buttonbugs/UA-AIAA-Payload-2026/data/rocket_20260618121819CDT/graph_pressure_temp.png

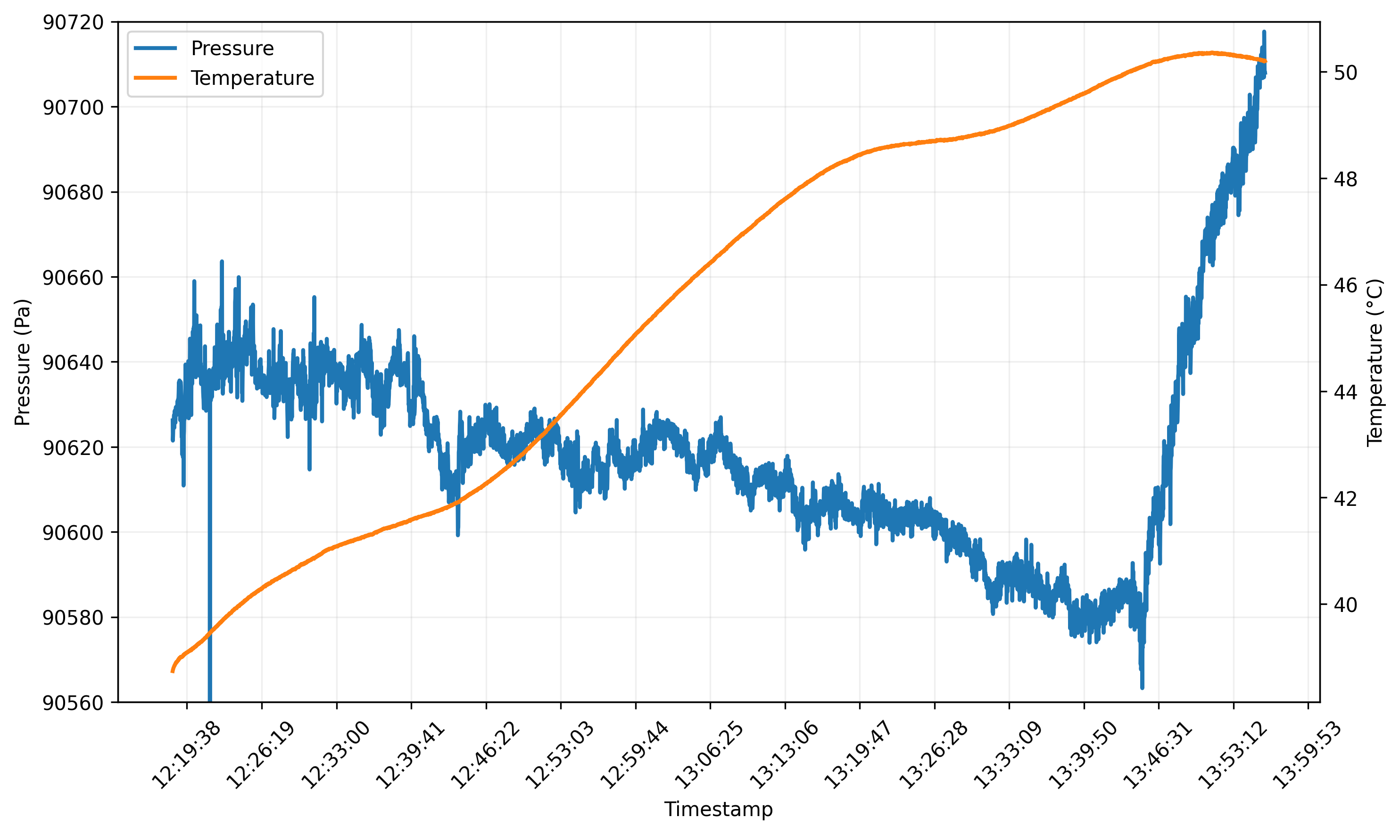
data/rocket_20260618121819CDT/graph_pressure_temp.png
