buttonbugs/UA-AIAA-Payload-2026/data/rocket_20260618121819CDT/graph_ultrasonic.png

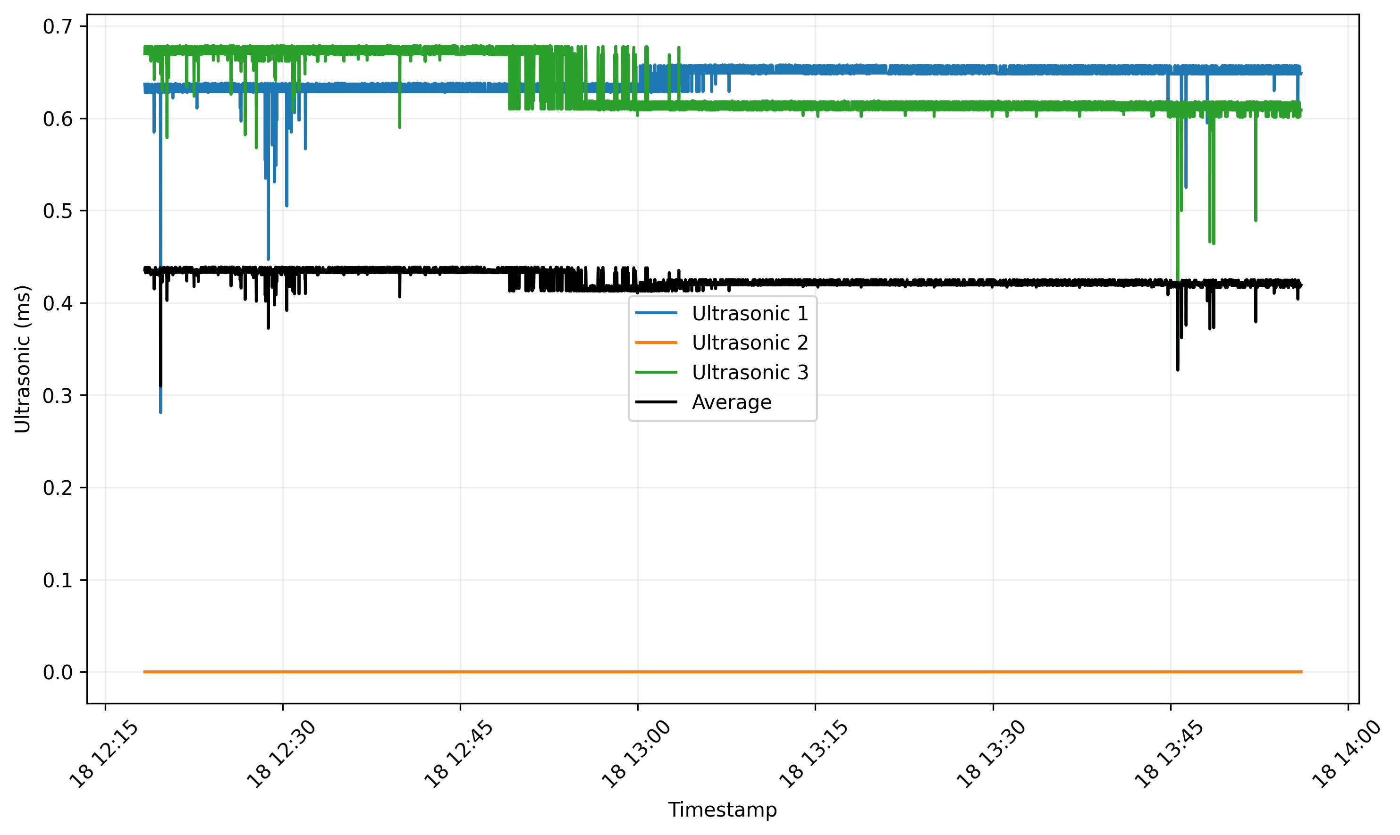
data/rocket_20260618121819CDT/graph_ultrasonic.png
