buttonbugs/UA-AIAA-Payload-2026/data/testing_20260617142200CDT/DATA_000.CSV

Timestamp (ms) | Ozone (PPB) | Air quality (VOC) | Accelerometer X (milli-g) | Accelerometer Y (milli-g) | Accelerometer Z (milli-g) | Gyroscope X (deg/s) | Gyroscope Y (deg/s) | Gyroscope Z (deg/s) | Magnetometer X (uT) | Magnetometer Y (uT) | Magnetometer Z (uT) | IMU Temperature (C) | BME280 Temperature (C) | Pressure (Pa) | Humidity (%RH) | Ultrasonic 1 (ms) | Ultrasonic 2 (ms) | Ultrasonic 3 (ms) | Vibration 1 Period (ms) | Vibration 2 Period (ms)
Timestamp (ms) | Ozone (PPB) | Air quality (VOC) | Accelerometer X (milli-g) | Accelerometer Y (milli-g) | Accelerometer Z (milli-g) | Gyroscope X (deg/s) | Gyroscope Y (deg/s) | Gyroscope Z (deg/s) | Magnetometer X (uT) | Magnetometer Y (uT) | Magnetometer Z (uT) | IMU Temperature (C) | BME280 Temperature (C) | Pressure (Pa) | Humidity (%RH) | Ultrasonic 1 (ms) | Ultrasonic 2 (ms) | Ultrasonic 3 (ms) | Vibration 1 Period (ms) | Vibration 2 Period (ms)
1140 | 0 | 0 | -2.3681639E+02 | 1.0917969E+03 | 9.3261711E+01 | -5.7480917E+00 | -2.9312978E+00 | -4.4198475E+00 | -2.4000000E+01 | -2.1900002E+01 | -4.1400002E+01 | 2.8748526E+01 | 2.5780001E+01 | 9.0634344E+04 | 3.3261719E+01 | 6.9000000E-01 | 0.0000000E+00 | 6.4399999E-01 | 0 | 0
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
