buttonbugs/UA-AIAA-Payload-2026/data/testing_20260617142200CDT/DATA_001.CSV

Timestamp (ms) | Ozone (PPB) | Air quality (VOC) | Accelerometer X (milli-g) | Accelerometer Y (milli-g) | Accelerometer Z (milli-g) | Gyroscope X (deg/s) | Gyroscope Y (deg/s) | Gyroscope Z (deg/s) | Magnetometer X (uT) | Magnetometer Y (uT) | Magnetometer Z (uT) | IMU Temperature (C) | BME280 Temperature (C) | Pressure (Pa) | Humidity (%RH) | Ultrasonic 1 (ms) | Ultrasonic 2 (ms) | Ultrasonic 3 (ms) | Vibration 1 Period (ms) | Vibration 2 Period (ms)
Timestamp (ms) | Ozone (PPB) | Air quality (VOC) | Accelerometer X (milli-g) | Accelerometer Y (milli-g) | Accelerometer Z (milli-g) | Gyroscope X (deg/s) | Gyroscope Y (deg/s) | Gyroscope Z (deg/s) | Magnetometer X (uT) | Magnetometer Y (uT) | Magnetometer Z (uT) | IMU Temperature (C) | BME280 Temperature (C) | Pressure (Pa) | Humidity (%RH) | Ultrasonic 1 (ms) | Ultrasonic 2 (ms) | Ultrasonic 3 (ms) | Vibration 1 Period (ms) | Vibration 2 Period (ms)
1125 | 0 | 0 | -1.5673828E+02 | 8.7255853E+02 | 1.1425780E+02 | -7.3511453E+00 | -1.8091604E+00 | -1.5648855E+00 | -4.1850002E+01 | -2.2650002E+01 | -1.8150002E+01 | 3.1144669E+01 | 2.6730000E+01 | 9.0554000E+04 | 3.2184570E+01 | 6.9000000E-01 | 0.0000000E+00 | 6.5200001E-01 | 0 | 0
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
