buttonbugs/UA-AIAA-Payload-2026/data/testing_20260419195100MST/DATA_000.CSV

Timestamp (ms) | Ozone (PPB) | Air quality (VOC) | Accelerometer X (milli-g) | Accelerometer Y (milli-g) | Accelerometer Z (milli-g) | Gyroscope X (deg/s) | Gyroscope Y (deg/s) | Gyroscope Z (deg/s) | Magnetometer X (uT) | Magnetometer Y (uT) | Magnetometer Z (uT) | IMU Temperature (C) | BME280 Temperature (C) | Pressure (Pa) | Humidity (%RH) | Ultrasonic 1 (ms) | Ultrasonic 2 (ms) | Ultrasonic 3 (ms) | Vibration 1 Period (ms) | Vibration 2 Period (ms)
1123 | 0 | 0 | -4.2626950E+02 | 4.9316402E+01 | 9.0917963E+02 | 4.5038167E-01 | 2.6870229E+00 | -9.0839696E-01 | 4.1850002E+01 | 3.7950001E+01 | 1.5450001E+01 | 2.6448229E+01 | 2.3350000E+01 | 9.2841852E+04 | 2.4069336E+01 | 0.0000000E+00 | 6.7150002E+00 | 9.3000001E-01 | 0 | 0
1675 | 0 | 0 | -4.3701169E+02 | 4.9804684E+01 | 9.1113275E+02 | 2.1374045E-01 | -1.7099236E+00 | 4.5801526E-01 | 4.1700001E+01 | 3.7800003E+01 | 1.5150001E+01 | 2.6735765E+01 | 2.3410000E+01 | 9.2841742E+04 | 2.3991211E+01 | 0.0000000E+00 | 6.7220001E+00 | 9.3000001E-01 | 0 | 0
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
