buttonbugs/UA-AIAA-Payload-2026/data/testing_20260617142200CDT/DATA_002.CSV

Timestamp (ms) | Ozone (PPB) | Air quality (VOC) | Accelerometer X (milli-g) | Accelerometer Y (milli-g) | Accelerometer Z (milli-g) | Gyroscope X (deg/s) | Gyroscope Y (deg/s) | Gyroscope Z (deg/s) | Magnetometer X (uT) | Magnetometer Y (uT) | Magnetometer Z (uT) | IMU Temperature (C) | BME280 Temperature (C) | Pressure (Pa) | Humidity (%RH) | Ultrasonic 1 (ms) | Ultrasonic 2 (ms) | Ultrasonic 3 (ms) | Vibration 1 Period (ms) | Vibration 2 Period (ms)
82638 | 20 | 100 | -1.1035155E+02 | 1.0004882E+03 | -6.3476558E+00 | -1.1450382E-01 | 3.1374047E+00 | -3.3129771E+00 | -4.9050003E+01 | -2.3100000E+01 | -1.8600000E+01 | 3.2774044E+01 | 2.7549999E+01 | 9.0546648E+04 | 3.1083008E+01 | 6.9000000E-01 | 0.0000000E+00 | 6.6000003E-01 | 0 | 0
83785 | 20 | 100 | -1.0205077E+02 | 9.8046869E+02 | 7.3242183E+00 | 1.0992366E+00 | 1.1603054E+00 | -1.4885496E+00 | -4.9350002E+01 | -2.3100000E+01 | -1.8150002E+01 | 3.2726120E+01 | 2.7549999E+01 | 9.0545797E+04 | 3.1071289E+01 | 6.9900000E-01 | 0.0000000E+00 | 6.6000003E-01 | 0 | 0
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
