buttonbugs/UA-AIAA-Payload-2026/data/testing_20260617142200CDT/graph_density.png

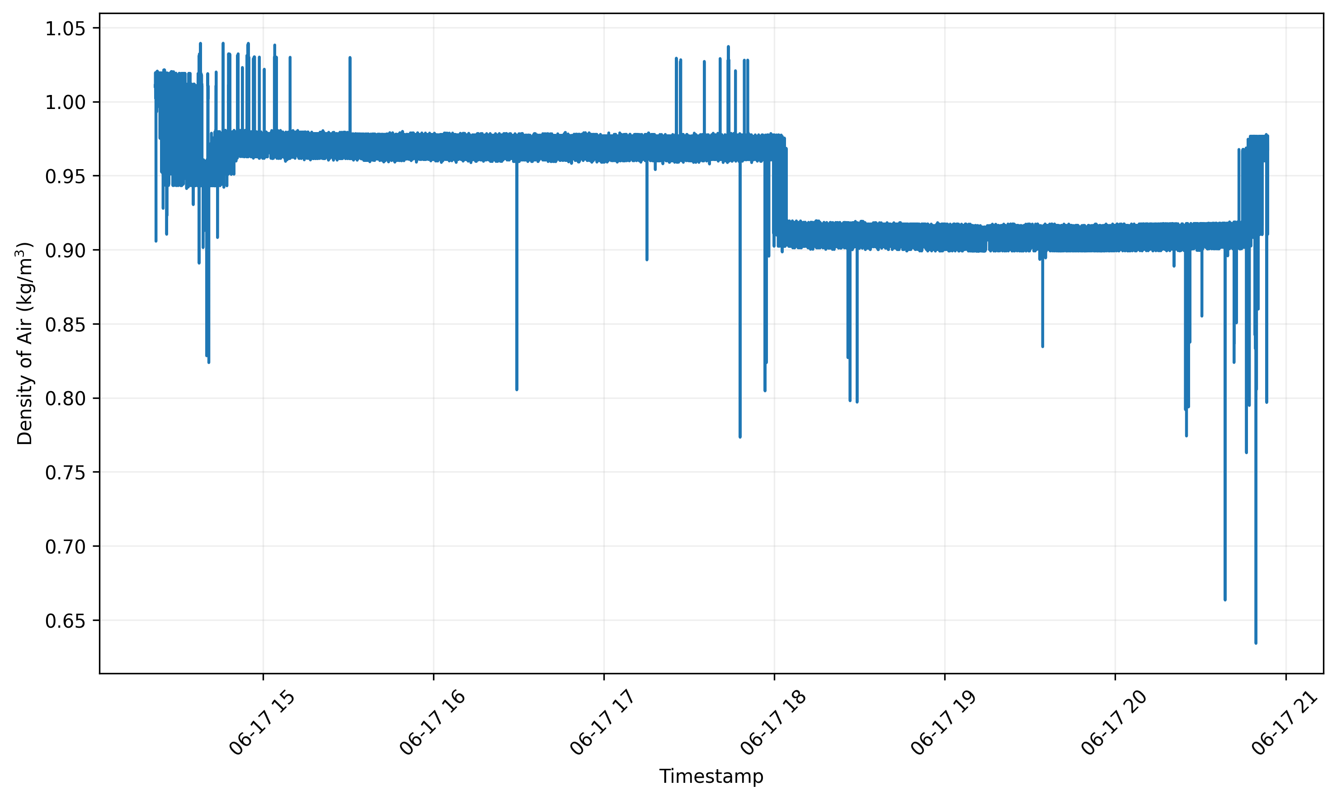
data/testing_20260617142200CDT/graph_density.png
