buttonbugs/UA-AIAA-Payload-2026/data/testing_20260617142200CDT/graph_pressure_temp.png

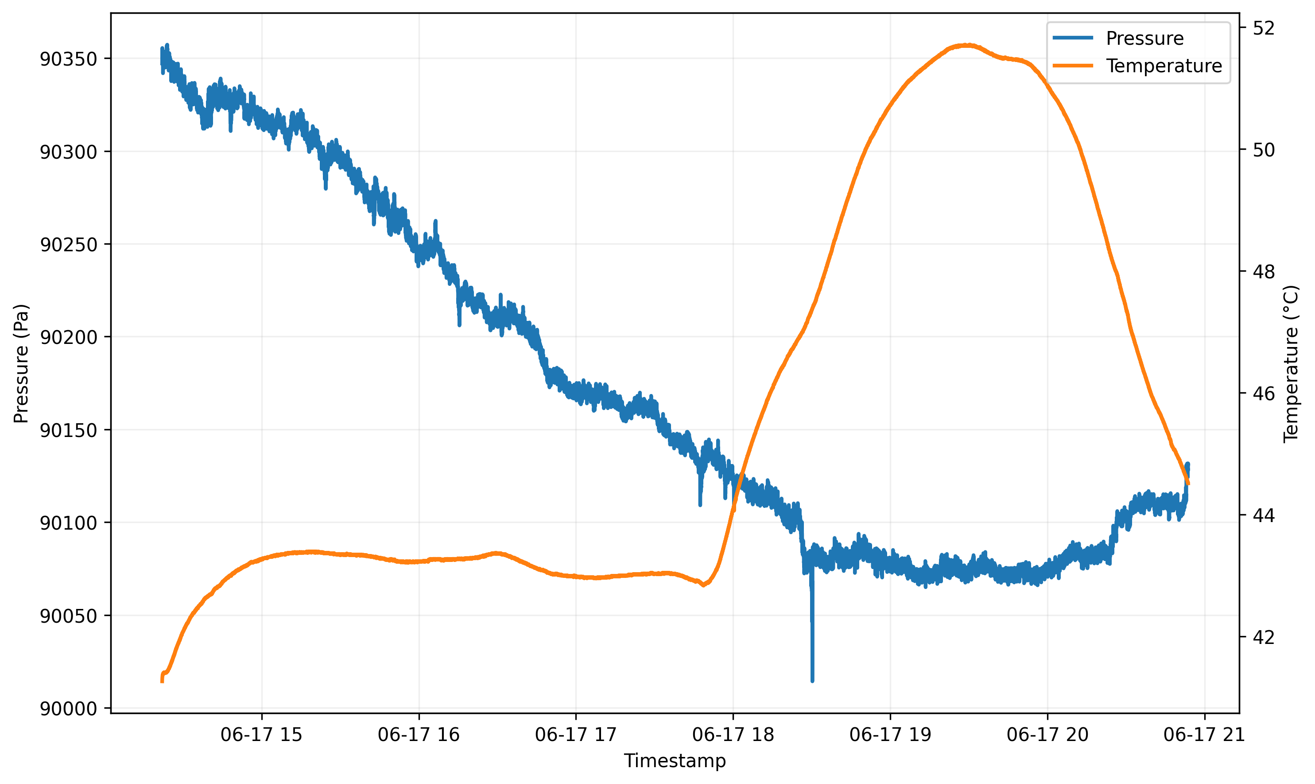
data/testing_20260617142200CDT/graph_pressure_temp.png
